misternoe/cheatbox/D-BRAKE - Haute42/R Series (UNTESTED BETA)/README.txt

CHEATBOX_PROJECT
D-BRAKE v2.0 for Haute42 R Series Controllers - BETA

/////////////
DISCLAIMER
/////////////

Use this product at your own risk. I am not responsible for any damages to you or your property. If you experience any pain or discomfort while using the D-BRAKE, please discontinue use immediately.

///////////////////////////////
COMPATIBILITY
///////////////////////////////

Unknown! This is basically a T-Series D-BRAKE with a shorter base. Design tweaks based on this post
https://x.com/helloneet/status/1823939648542138430

///////////////////////////////
THINGS TO KNOW BEFORE PRINTING
///////////////////////////////

UNTESTED

/////////////
PRINTER SETTINGS
/////////////

IMPORTANT -- Printing Orientation
The D-BRAKE looks best when printed upright, with the mount parallel to the build plate. Check the reference photo in the GitHub directory.

Infill: 10% to 25%

Layer height: 0.2 minimum

Build Plate Adhesion Type: Brim highly recommended due to the verticality of the printing orientation

Supports: Yes - Touching Buildplate

/////////////
PRINTING SERVICES: SIZING WHEN UPLOADED
/////////////

TBD

/////////////
INSTALLATION
/////////////
1. Remove plunger or keycap (see manufacturer for info on this if needed)
2. Mount D-BRAKE onto the button/microswitch

/////////////
REPORT BACK + ENJOY
/////////////

Let me know how you're enjoying this on Twitter or here on GitHub. Constructive feedback is always welcome. Give me a follow on Twitter @noe_perez_ to keep up with other projects like this and new Cheatbox Project designs for the Snackbox Micro, Hit Box, and other all-button controllers.

https://github.com/misternoe/cheatbox

/////////////
SHOUTOUTS
/////////////

@junkfoodarcades for making great products supporting the modding community

@NoGoodCitizen for spreading the gospel of the Cheatbox_Project to the FGC

Robear512 (@236Robear) for their dedication to bringing us a Qanba Gravity D-BRAKE

@helloneet for the R16 references

Anyone's that supported my on etsy or spread the word about cheatbox_project products!
