misternoe/cheatbox/D-BRAKE - Haute42/G Series/README.txt

CHEATBOX_PROJECT
D-BRAKE v2.0 for Haute42 G Series Controllers

/////////////
DISCLAIMER
/////////////

Use this product at your own risk. I am not responsible for any damages to you or your property. If you experience any pain or discomfort while using the D-BRAKE, please discontinue use immediately.

///////////////////////////////
COMPATIBILITY
///////////////////////////////

Works with:
G13/G16

Incompatible or unknown:
M-Series and S-Series - unknown but likely this is too large for it
T-Series - incompatible

///////////////////////////////
THINGS TO KNOW BEFORE PRINTING
///////////////////////////////

All testing conducted on a Haute42 G16

All test printing with a Bambu X1 Carbon

Materials tested:
PETG: Excellent output

/////////////
PRINTER SETTINGS
/////////////

IMPORTANT -- Printing Orientation
The D-BRAKE looks best when printed upright, with the mount parallel to the build plate. Check the reference photo in the GitHub directory.

Infill: 10% to 25%

Layer height: 0.2 minimum

Build Plate Adhesion Type: Brim highly recommended due to the verticality of the printing orientation

Supports: Yes - Touching Buildplate

/////////////
FINISHING
/////////////
If your printer is unable to produce a smooth print, it is recommended to sand down this print to provide a smoother and more comfortable surface. Use a high grit wet sandpaper (600 or higher). Please remember to take proper safety precautions to avoid inhalation by yourself and others in your vicinity.

/////////////
PRINTING SERVICES: SIZING WHEN UPLOADED
/////////////

TBD

/////////////
INSTALLATION
/////////////
1. Remove plunger or keycap (see manufacturer for info on this if needed)
2. Mount D-BRAKE onto the button/microswitch

/////////////
REPORT BACK + ENJOY
/////////////

Let me know how you're enjoying this on Twitter or here on GitHub. Constructive feedback is always welcome. Give me a follow on Twitter @noe_perez_ to keep up with other projects like this and new Cheatbox Project designs for the Snackbox Micro, Hit Box, and other all-button controllers.

https://github.com/misternoe/cheatbox

/////////////
SHOUTOUTS
/////////////

@junkfoodarcades for making great products supporting the modding community

@NoGoodCitizen for spreading the gospel of the Cheatbox_Project to the FGC

Robear512 (@236Robear) for their dedication to bringing us a Qanba Gravity D-BRAKE

@brainpipeFGC for the idea to explore and workshop the potential of the D-BRAKE + G16

Anyone's that supported my on etsy or spread the word about cheatbox_project products!
