misternoe/cheatbox/Snackbox Micro/ACCESSORIES/FOOTSIE/Original Artwork Case/README.txt

CHEATBOX_PROJECT
FOOTSIE v1.0
For Snackbox Micro Artwork Case

/////////////
DISCLAIMER
/////////////

Use this product at your own risk. I am not responsible for any damages to you or your property.

///////////////////////////////
THINGS TO KNOW BEFORE PRINTING
///////////////////////////////

All testing conducted on a Dremel DigiLab 3D45 with a stock pre-2023 Snackbox Micro Artwork Case.

Materials tested:
PLA: Excellent output

Important:
Make sure that your 3D printer is configured properly before printing this accessory. Due to the thin nature of this product, ensuring that the first few layers print cleanly will ensure a stronger end product.

/////////////
PRINTER SETTINGS
/////////////
15% Infill recommended

Layer height
0.3 or 0.34 look great and print quickly. 0.34 looks best to me personally.

/////////////
SIZING
/////////////

FOOTSIE-LEFT
X = 168mm
Y = 127.25mm
Z = 15mm

FOOTSIE-RIGHT
X = 168mm
Y = 127.25mm
Z = 15mm

FOOTSIE-SINGLE
X = 336mm
Y = 127.25mm
Z = 15mm

/////////////
INSTALLATION
/////////////
1. Unscrew backplate of Snackbox Micro

2. Install The Footsie between backplate and Snackbox Micro Artwork Case. The Footsie is to be “sandwiched” between these two components.

3. Insert screws and be sure to not over-tighten

/////////////
REPORT BACK + ENJOY
/////////////

Let me know how testing is going on Twitter or here on GitHub. Give me a follow on Twitter @noe_perez_ to keep up with other projects like this and new Cheatbox Project designs for the Snackbox Micro and other all-button controllers.

https://github.com/misternoe/cheatbox
