misternoe/cheatbox/Snackbox Micro/ACCESSORIES/FOOTSIE/FOOTSIE - ORIGINAL/Micro XL/README.txt

CHEATBOX_PROJECT
FOOTSIE v1.0
For Snackbox Micro XL Case

/////////////
DISCLAIMER
/////////////

Use this product at your own risk. I am not responsible for any damages to you or your property.

///////////////////////////////
THINGS TO KNOW BEFORE PRINTING
///////////////////////////////

All testing conducted on a Dremel DigiLab 3D45 with a stock 2023 Snackbox Micro XL.

Materials tested:
PLA: Excellent output

Important:
Make sure that your 3D printer is configured properly before printing this accessory. Due to the thin nature of this product, ensuring that the first few layers print cleanly will ensure a stronger end product.

/////////////
PRINTER SETTINGS
/////////////
15% Infill recommended

Layer height
0.3 or 0.34 look great and print quickly. 0.34 looks best to me personally.

/////////////
SIZING
/////////////

FOOTSIE-LEFT
X = 199.25mm
Y = 143.875mm
Z = 13.625mm

FOOTSIE-RIGHT
X = 199.25mm
Y = 143.875mm
Z = 13.625mm

/////////////
INSTALLATION
/////////////
1. Unscrew backplate of Snackbox Micro XL Case

2. Install The Footsie between backplate and Snackbox Micro XL Case. The Footsie is to be “sandwiched” between these two components.

3. Insert screws and be sure to not over-tighten

/////////////
REPORT BACK + ENJOY
/////////////

Let me know how testing is going on Twitter or here on GitHub. Give me a follow on Twitter @noe_perez_ to keep up with other projects like this and new Cheatbox Project designs for the Snackbox Micro and other all-button controllers.

https://github.com/misternoe/cheatbox
