misternoe/cheatbox/Snackbox Micro/ACCESSORIES/FOOTSIE/FOOTSIE - ORIGINAL/New Artwork Case and One Piece Case/README.txt

CHEATBOX_PROJECT
FOOTSIE v1.0
For Snackbox Micro One Piece Case

/////////////
DISCLAIMER
/////////////

Use this product at your own risk. I am not responsible for any damages to you or your property.

///////////////////////////////
THINGS TO KNOW BEFORE PRINTING
///////////////////////////////

All testing conducted on a Dremel DigiLab 3D45 with a stock 2023 Snackbox One Piece Case - Clear.

Materials tested:
PLA: Excellent output

Important:
Make sure that your 3D printer is configured properly before printing this accessory. Due to the thin nature of this product, ensuring that the first few layers print cleanly will ensure a stronger end product.

/////////////
PRINTER SETTINGS
/////////////
15% Infill recommended

Layer height
0.3 or 0.34 look great and print quickly. 0.34 looks best to me personally.

/////////////
SIZING
/////////////

FOOTSIE-LEFT
X = 166.125mm
Y = 129mm
Z = 14.5mm

FOOTSIE-RIGHT
X = 166.25mm
Y = 129mm
Z = 14.5mm

FOOTSIE-SINGLE
X = 330mm
Y = 129mm
Z = 14.5mm

/////////////
INSTALLATION
/////////////
1. Unscrew backplate of Snackbox Micro One Piece Case

2. Install The Footsie between backplate and Snackbox Micro One Piece Case. The Footsie is to be “sandwiched” between these two components.

3. Insert screws and be sure to not over-tighten

/////////////
REPORT BACK + ENJOY
/////////////

Let me know how testing is going on Twitter or here on GitHub. Give me a follow on Twitter @noe_perez_ to keep up with other projects like this and new Cheatbox Project designs for the Snackbox Micro and other all-button controllers.

https://github.com/misternoe/cheatbox
