misternoe/cheatbox/Hitbox/cheatbox-hitbox-input-trainer.png

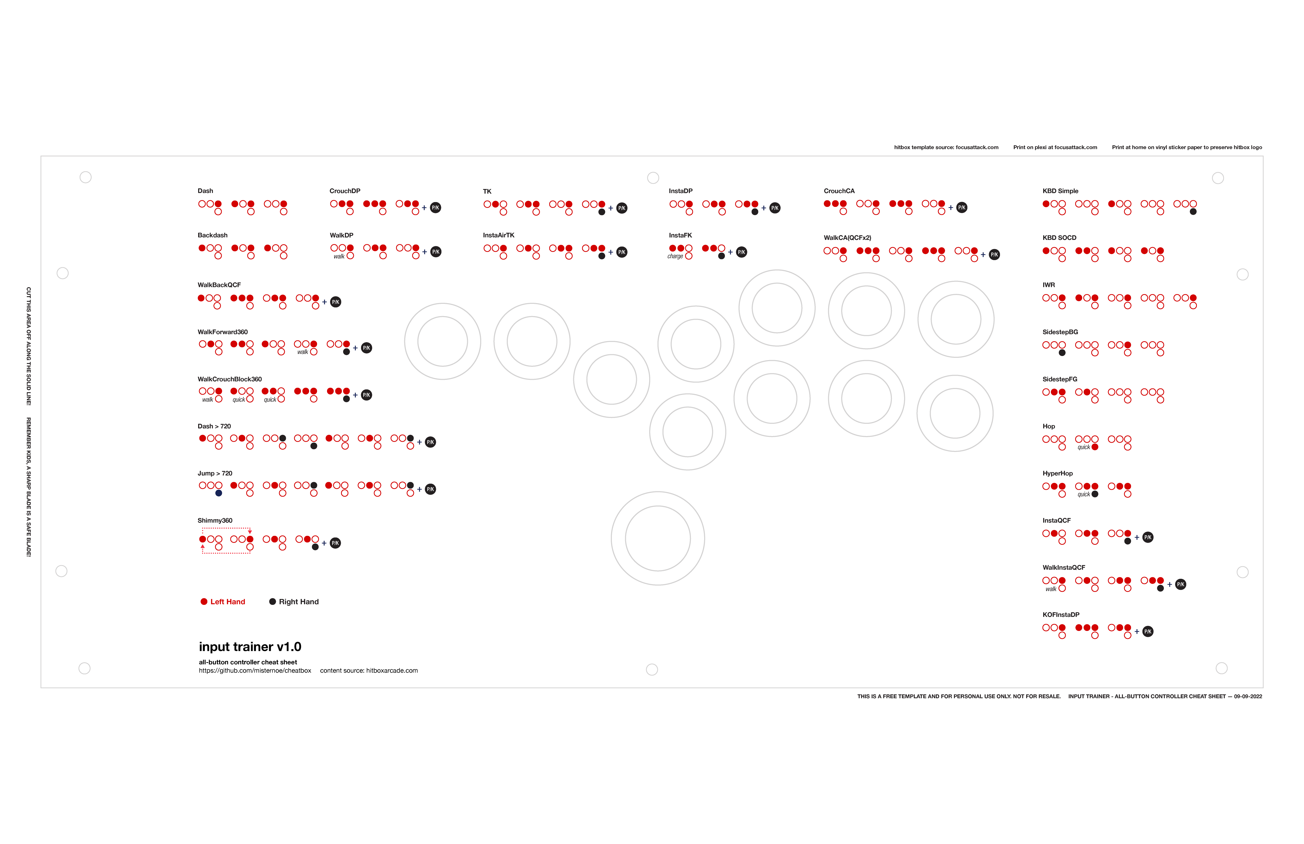
Hitbox/cheatbox-hitbox-input-trainer.png
