misternoe/cheatbox/Snackbox Micro/SFV/cheatboxmicro-sfv-jur-8.5x11-300DPI.png

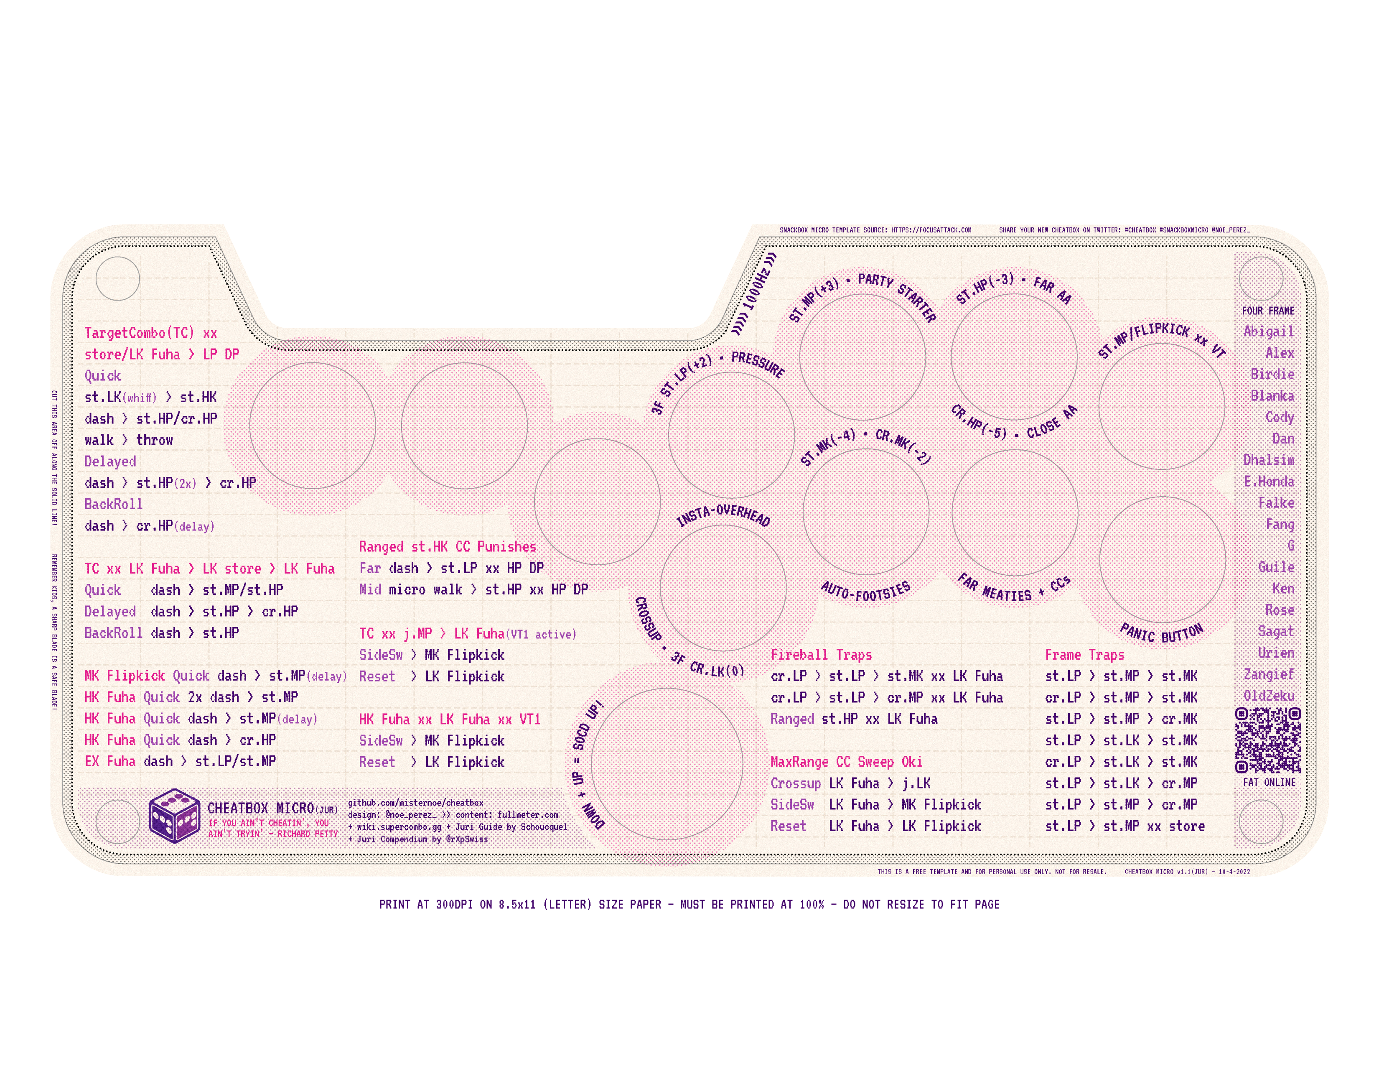
Snackbox Micro/SFV/cheatboxmicro-sfv-jur-8.5x11-300DPI.png
