misternoe/cheatbox/Snackbox Micro/SG/cheatboxmicro-sg-bgbnd-8.5x11-300DPI.png

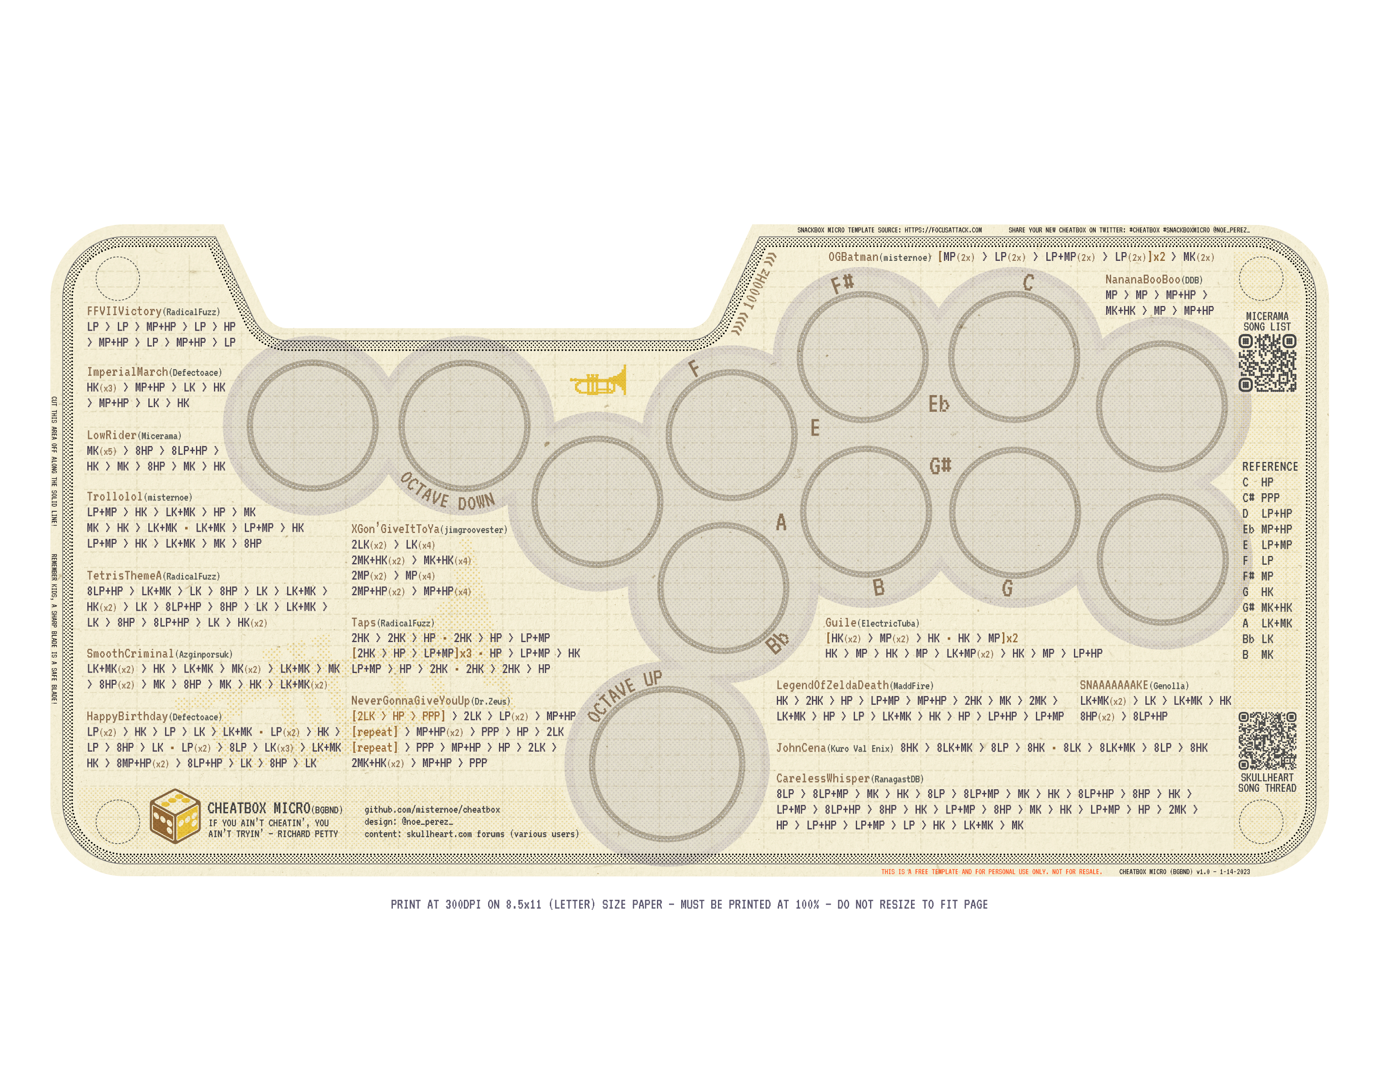
Snackbox Micro/SG/cheatboxmicro-sg-bgbnd-8.5x11-300DPI.png
