misternoe/cheatbox/Snackbox Micro/SOCD/cheatboxmicro-socd-brbrshp-classic-8.5x11-300DPI.png

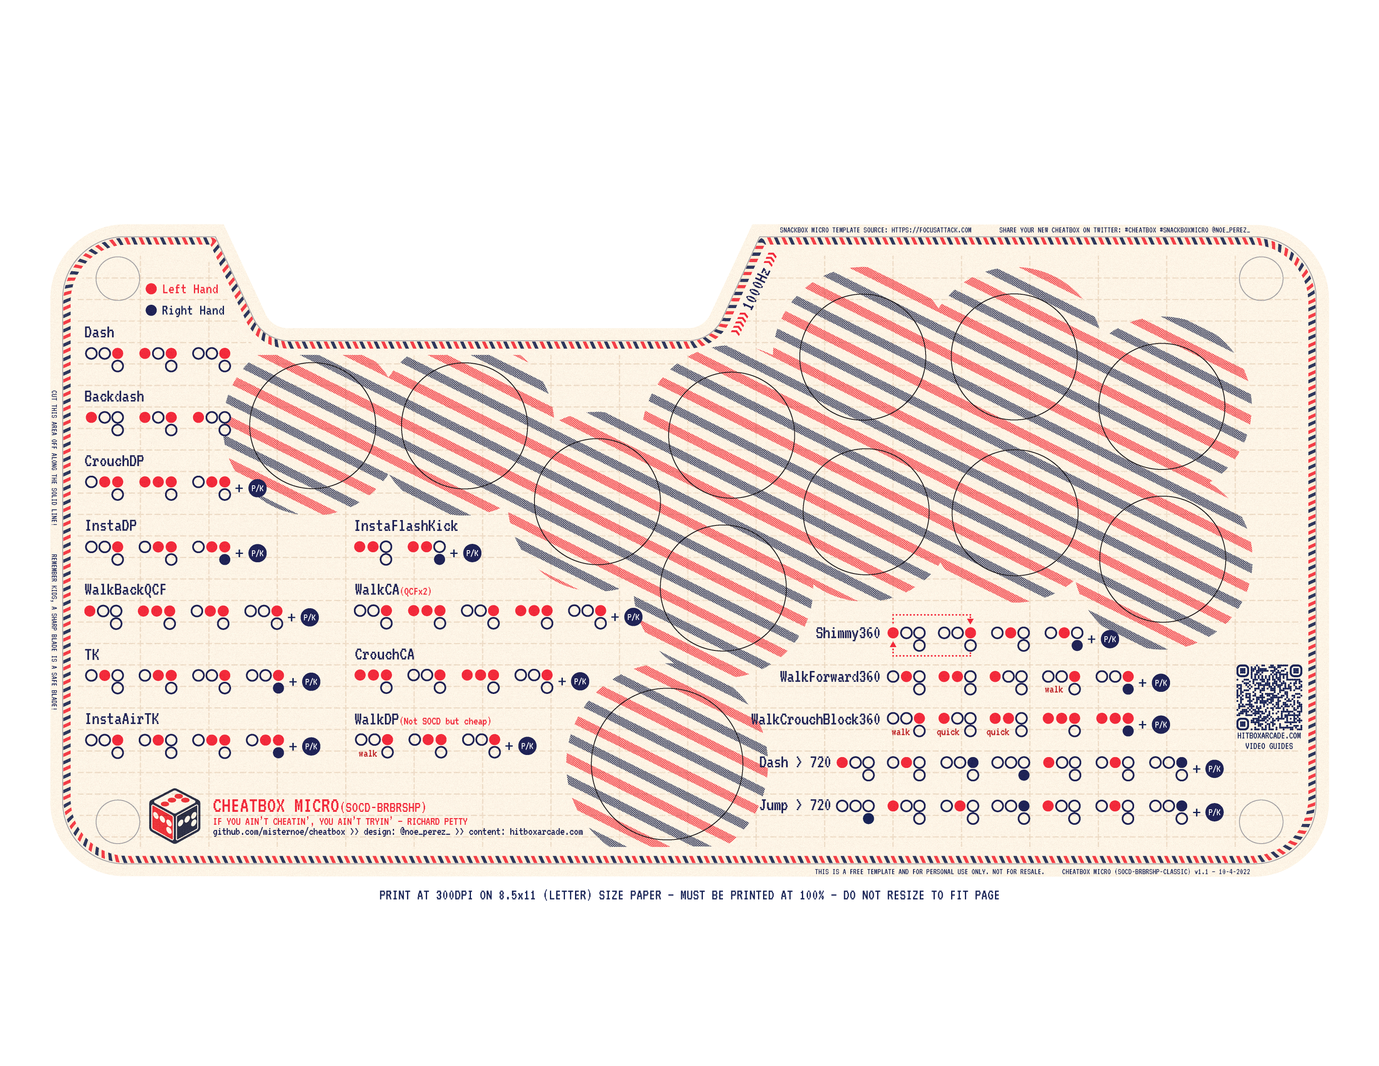
Snackbox Micro/SOCD/cheatboxmicro-socd-brbrshp-classic-8.5x11-300DPI.png
