misternoe/cheatbox/D-BRAKE/remix-cheatbox-project-dbrake-qanba-gravity-24mm-size11.stl

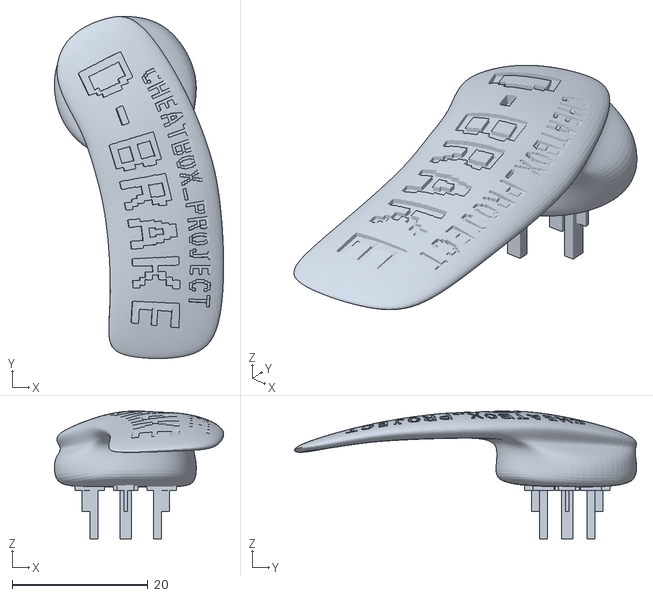
[picture p29: CAD file, 2024-03-22]
D-BRAKE/remix-cheatbox-project-dbrake-qanba-gravity-24mm-size11.stl
24.9 x 50.3 x 18.8
