misternoe/cheatbox/FOOTSIE - NEW/cheatbox-project-footsie-left.stl

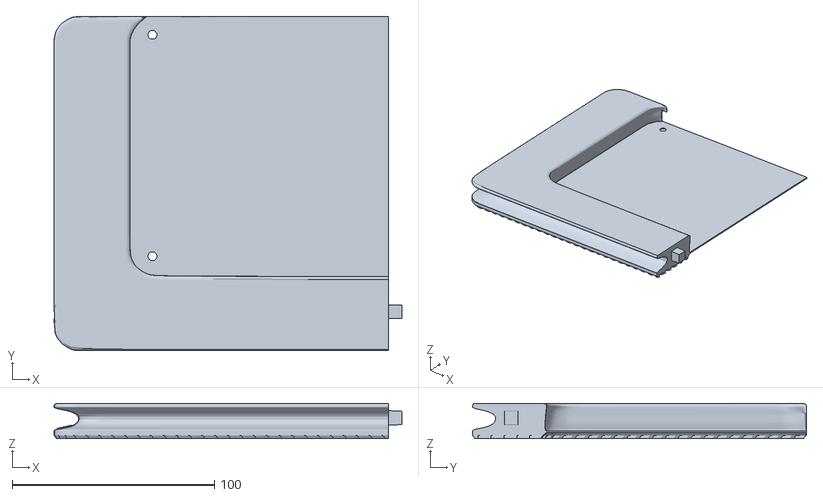
[picture p30: CAD file, 2025-10-26]
FOOTSIE - NEW/cheatbox-project-footsie-left.stl
172.1 x 165.1 x 17.5
