misternoe/cheatbox/Haute42 B16/cheatboxproject-B16-faceplate-face-up.stl

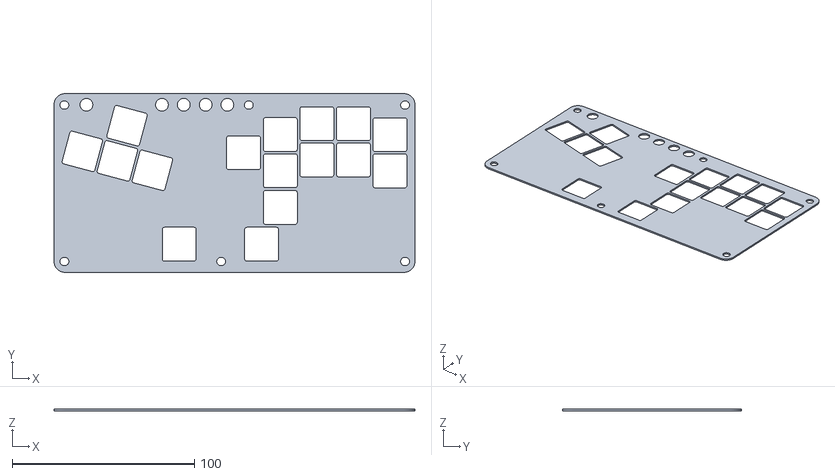
[picture p31: CAD file, 2025-02-02]
Haute42 B16/cheatboxproject-B16-faceplate-face-up.stl
198.0 x 98.0 x 0.96
