misternoe/cheatbox/Snackbox Micro/ACCESSORIES/FOOTSIE/FOOTSIE - ORIGINAL/Micro XL/micro-xl-footsie-right.stl

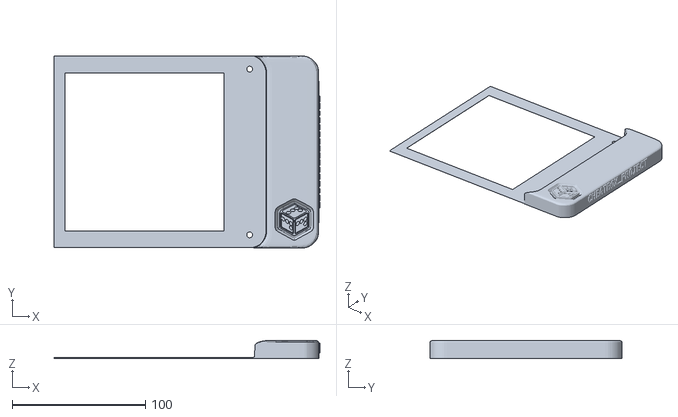
[picture p32: CAD file, 2023-04-07]
Snackbox Micro/ACCESSORIES/FOOTSIE/FOOTSIE - ORIGINAL/Micro XL/micro-xl-footsie-right.stl
199.3 x 143.9 x 13.6
