misternoe/cheatbox/Snackbox Micro/ACCESSORIES/FOOTSIE/FOOTSIE - ORIGINAL/Needs Testing/OG Snackbox Micro/og-micro-footsie-right.stl

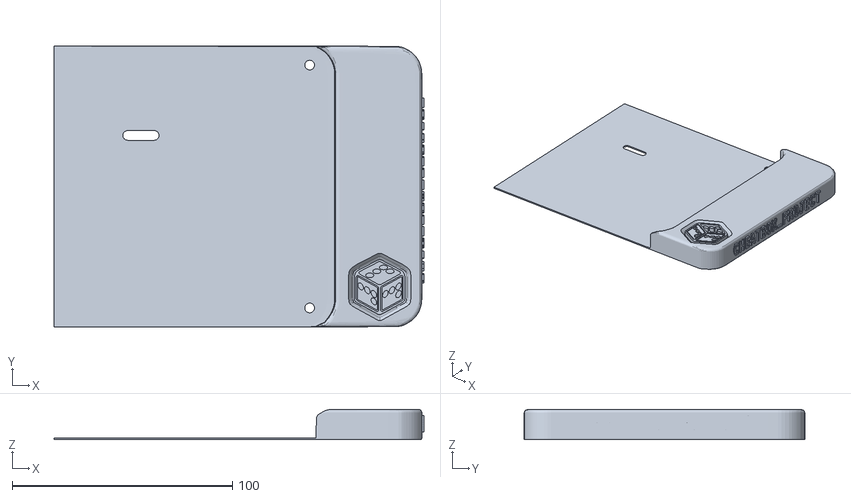
[picture p33: CAD file, 2023-03-16]
Snackbox Micro/ACCESSORIES/FOOTSIE/FOOTSIE - ORIGINAL/Needs Testing/OG Snackbox Micro/og-micro-footsie-right.stl
168.0 x 127.4 x 13.8
