misternoe/cheatbox/Snackbox Micro/ACCESSORIES/FOOTSIE/Original Artwork Case/original-artworkcase-footsie-left.stl

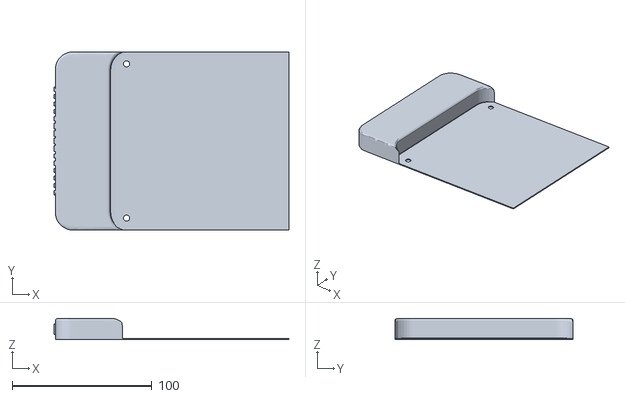
[picture p34: CAD file, 2023-03-15]
Snackbox Micro/ACCESSORIES/FOOTSIE/Original Artwork Case/original-artworkcase-footsie-left.stl
168.0 x 127.4 x 15.1
