misternoe/cheatbox/SWORL/Hole Plugs/sw-plug-below-artwork.stl

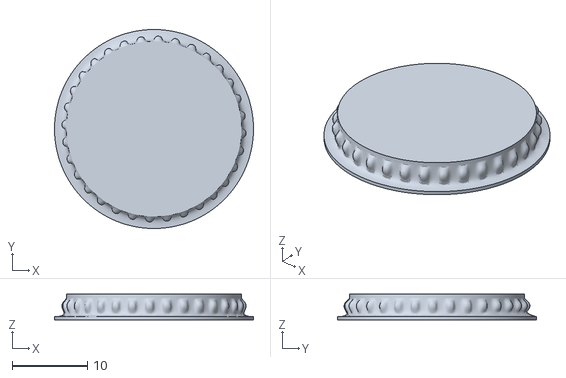
[picture p35: CAD file, 2025-09-05]
SWORL/Hole Plugs/sw-plug-below-artwork.stl
26.5 x 26.5 x 3.41
