misternoe/cheatbox/D-BRAKE - Flashtap/dbrake-flashtap24-09mm-CE.stl

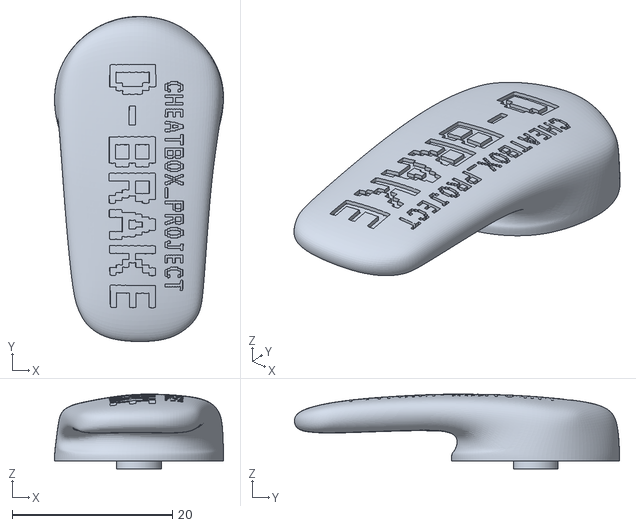
[picture p36: CAD file, 2026-08-28]
D-BRAKE - Flashtap/dbrake-flashtap24-09mm-CE.stl
21.1 x 40.6 x 9.33
