misternoe/cheatbox/D-BRAKE/remix-cheatbox-project-dbrake-qanba-gravity-30mm-size11.stl

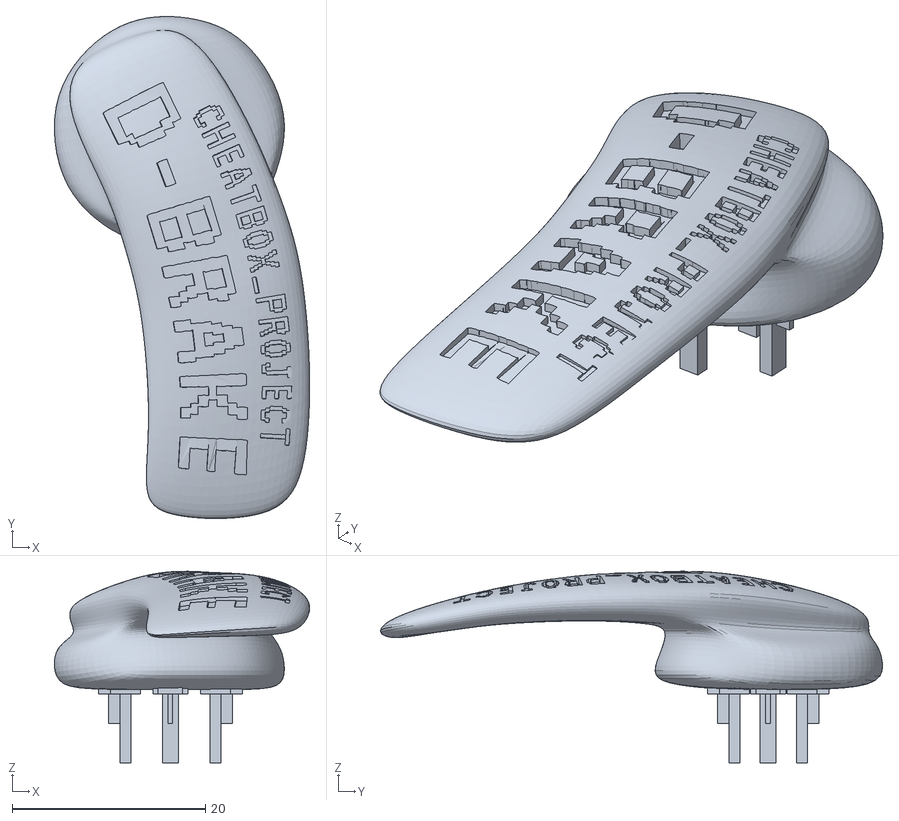
[picture p37: CAD file, 2024-03-12]
D-BRAKE/remix-cheatbox-project-dbrake-qanba-gravity-30mm-size11.stl
26.4 x 52.0 x 19.8
