misternoe/cheatbox/Snackbox Micro/ACCESSORIES/FOOTSIE/FOOTSIE - ORIGINAL/Needs Testing/OG Snackbox Micro/og-micro-footsie-left.stl

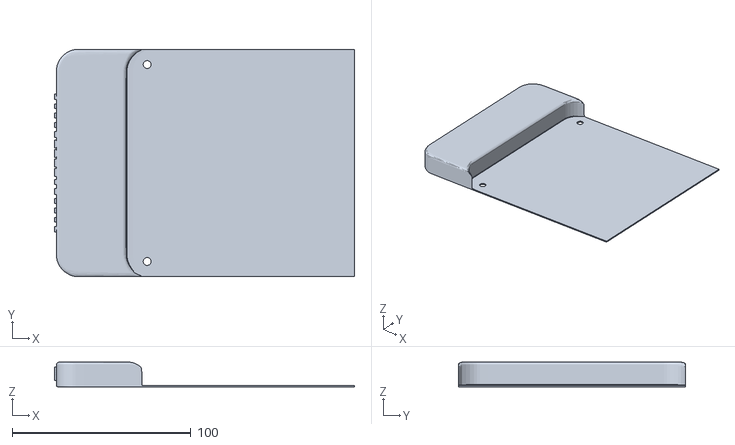
[picture p38: CAD file, 2023-03-16]
Snackbox Micro/ACCESSORIES/FOOTSIE/FOOTSIE - ORIGINAL/Needs Testing/OG Snackbox Micro/og-micro-footsie-left.stl
168.0 x 127.4 x 13.8
