misternoe/cheatbox/D-BRAKE/remix-robear512-dbrake-qanba-gravity-30mm.stl

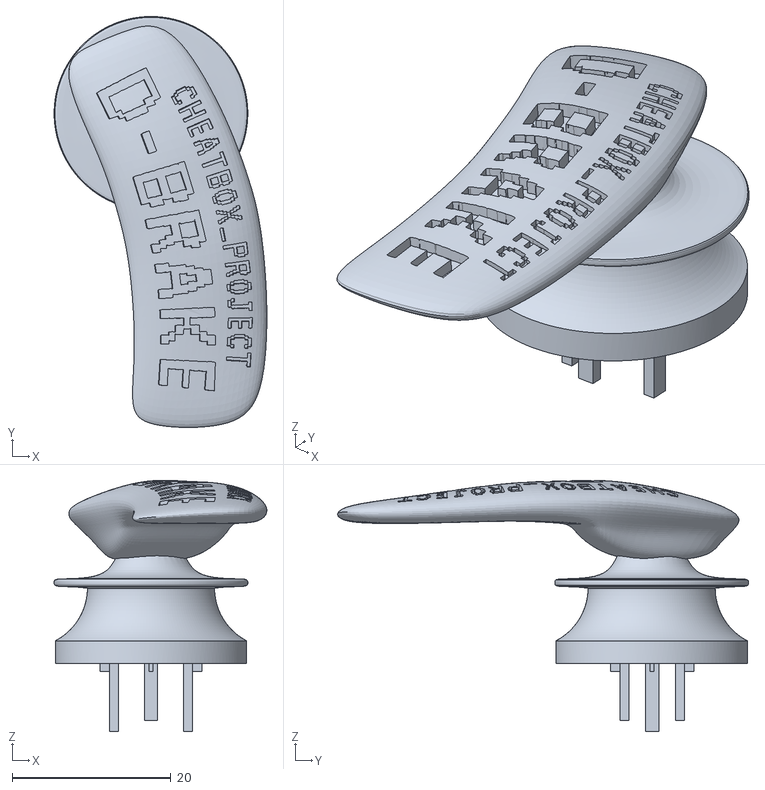
[picture p40: CAD file, 2024-03-12]
D-BRAKE/remix-robear512-dbrake-qanba-gravity-30mm.stl
26.8 x 51.7 x 31.6
