misternoe/cheatbox/D-BRAKE/cheatbox-project-dbrake-snackboxmicro-kailh-choc-v1-thickerstem.stl

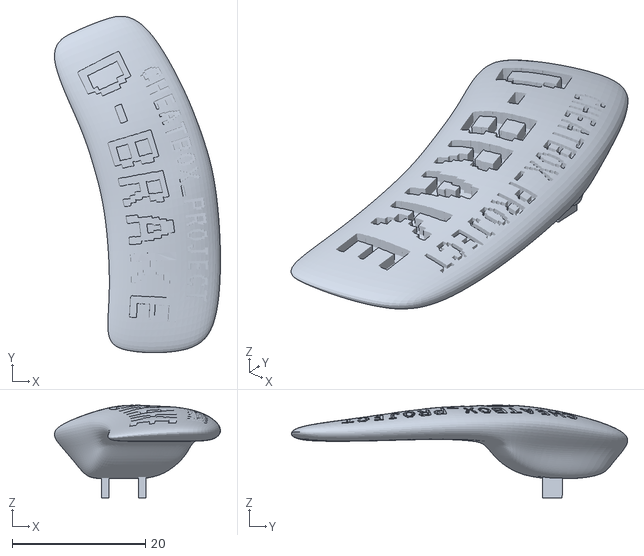
[picture p41: CAD file, 2023-06-09]
D-BRAKE/cheatbox-project-dbrake-snackboxmicro-kailh-choc-v1-thickerstem.stl
24.9 x 50.5 x 13.9
