misternoe/cheatbox/D-BRAKE/cheatbox-project-dbrake-sanwa-seimitsu-30mm-size10.stl

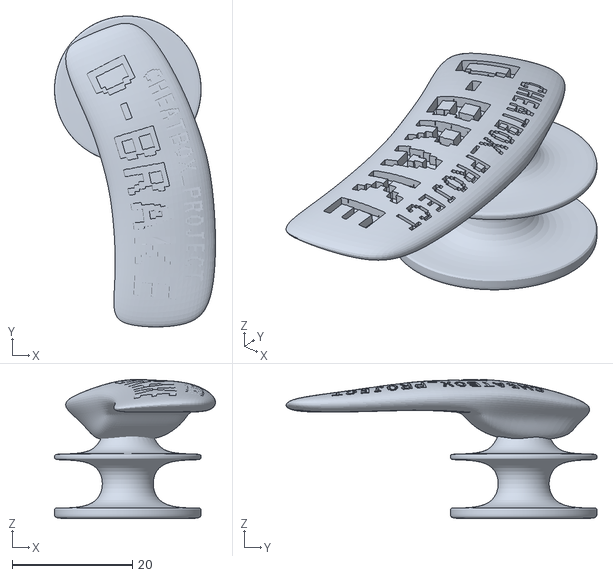
[picture p42: CAD file, 2023-06-02]
D-BRAKE/cheatbox-project-dbrake-sanwa-seimitsu-30mm-size10.stl
26.8 x 51.7 x 23.1
