misternoe/cheatbox/D-BRAKE/cheatbox-project-dbrake-sanwa-seimitsu-30mm-size11.stl

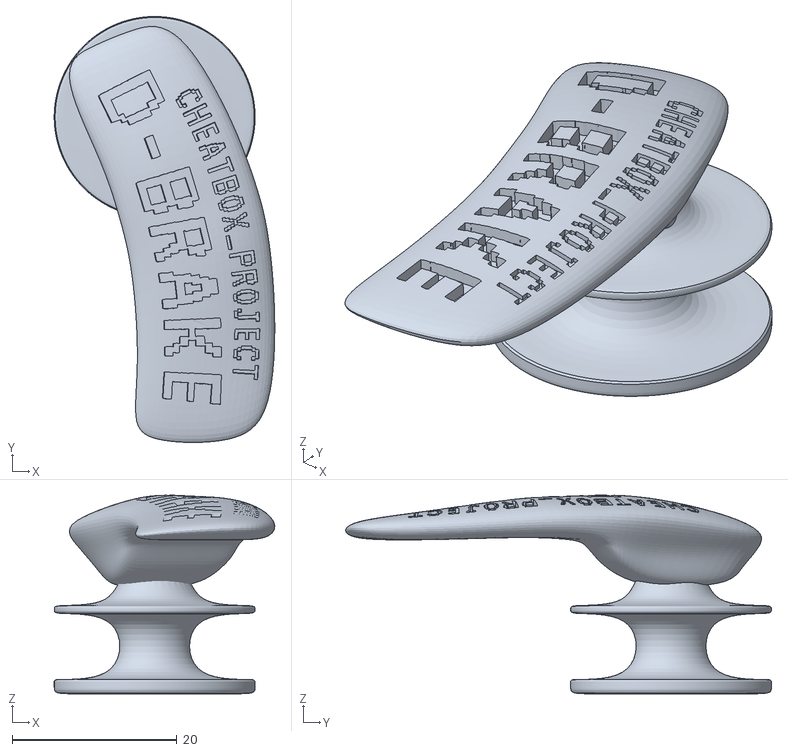
[picture p43: CAD file, 2023-06-02]
D-BRAKE/cheatbox-project-dbrake-sanwa-seimitsu-30mm-size11.stl
26.8 x 51.7 x 24.1
