misternoe/cheatbox/D-BRAKE/cheatbox-project-dbrake-cherrymx-10mm.stl

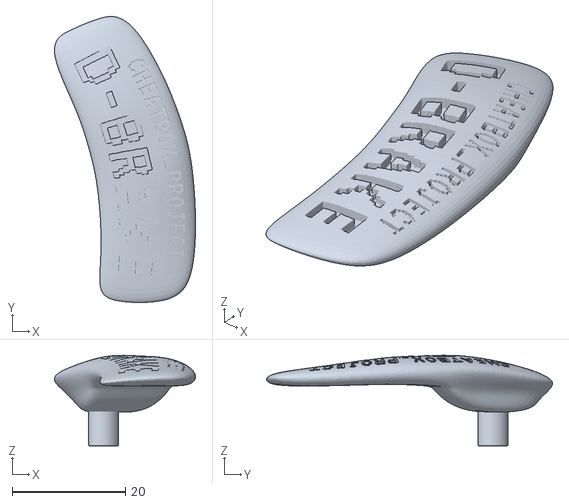
[picture p44: CAD file, 2023-05-29]
D-BRAKE/cheatbox-project-dbrake-cherrymx-10mm.stl
24.9 x 50.5 x 16.0
