misternoe/cheatbox/D-BRAKE/cheatbox-project-dbrake-cherrymx-11mm.stl

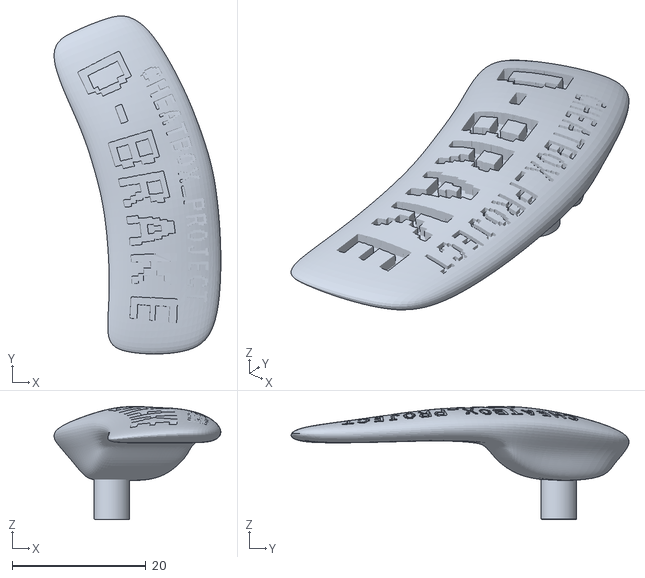
[picture p45: CAD file, 2023-05-29]
D-BRAKE/cheatbox-project-dbrake-cherrymx-11mm.stl
24.9 x 50.5 x 16.9
