misternoe/cheatbox/D-BRAKE/dbrake-gravity-printing-orientation.jpg

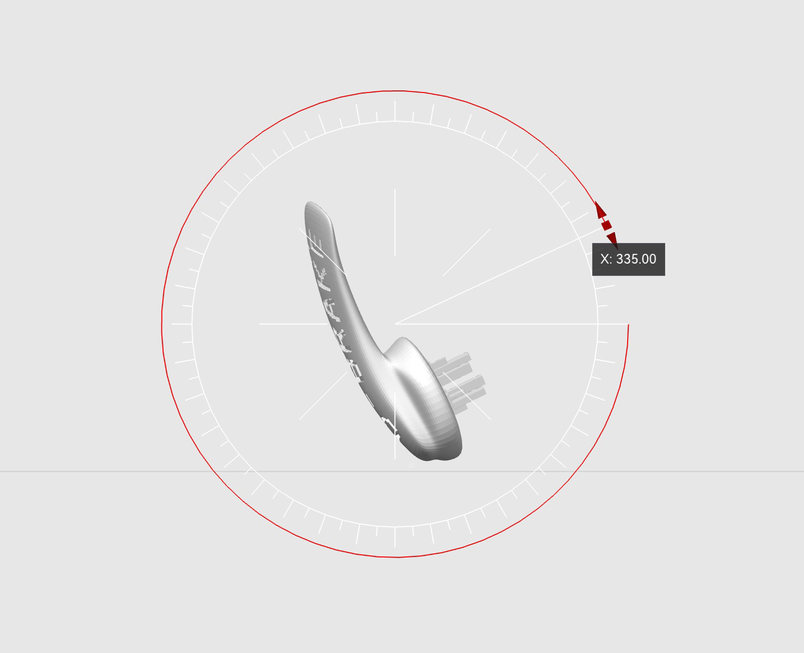
D-BRAKE/dbrake-gravity-printing-orientation.jpg
