misternoe/cheatbox/D-BRAKE/dbrake-printing-orientation.jpg

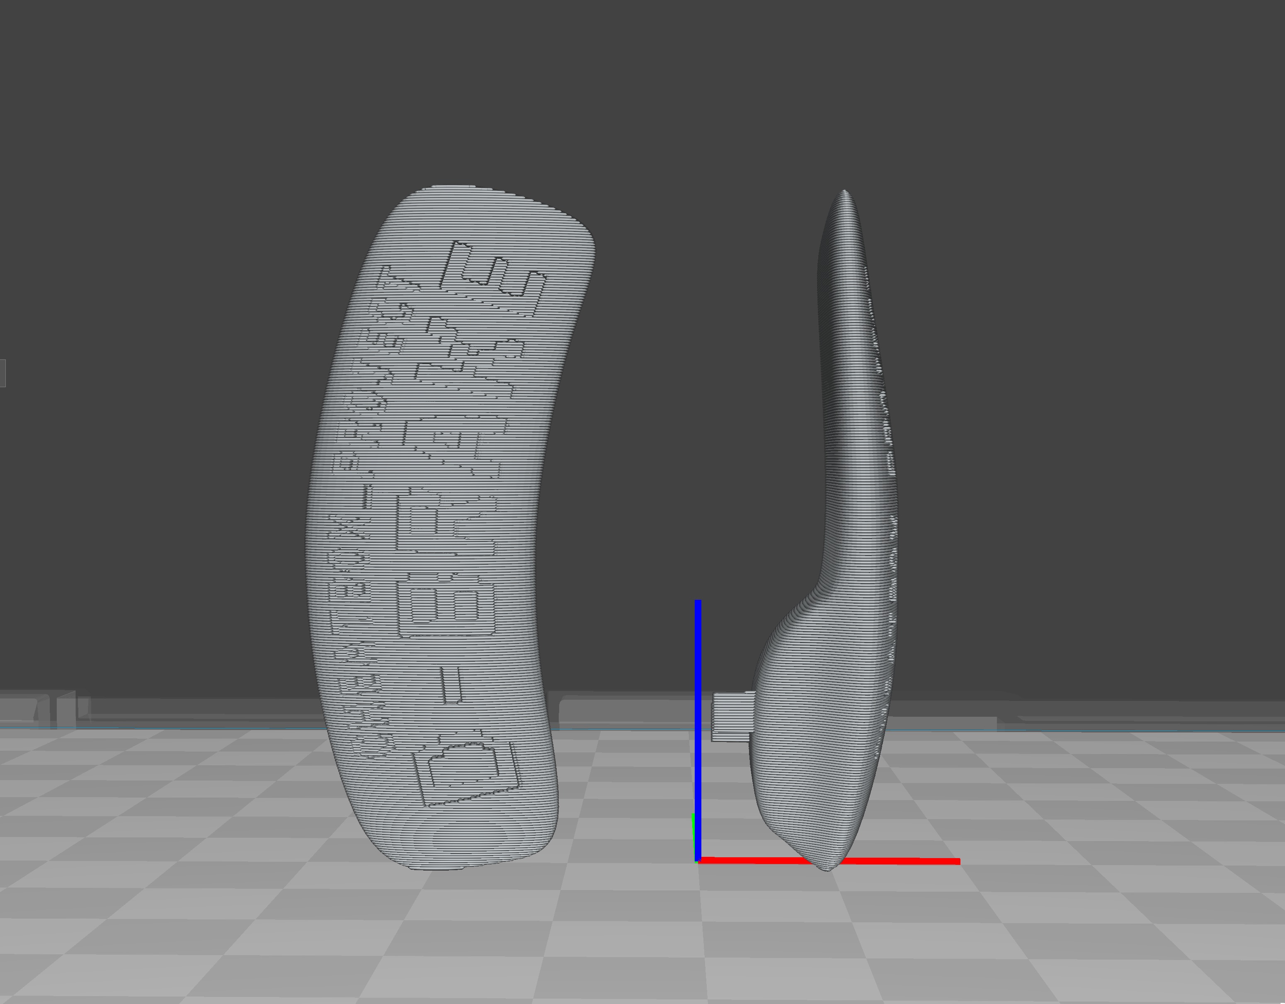
D-BRAKE/dbrake-printing-orientation.jpg
