misternoe/cheatbox/FOOTSIE - NEW/footsie-printing-orientation-for-small-printers.jpg

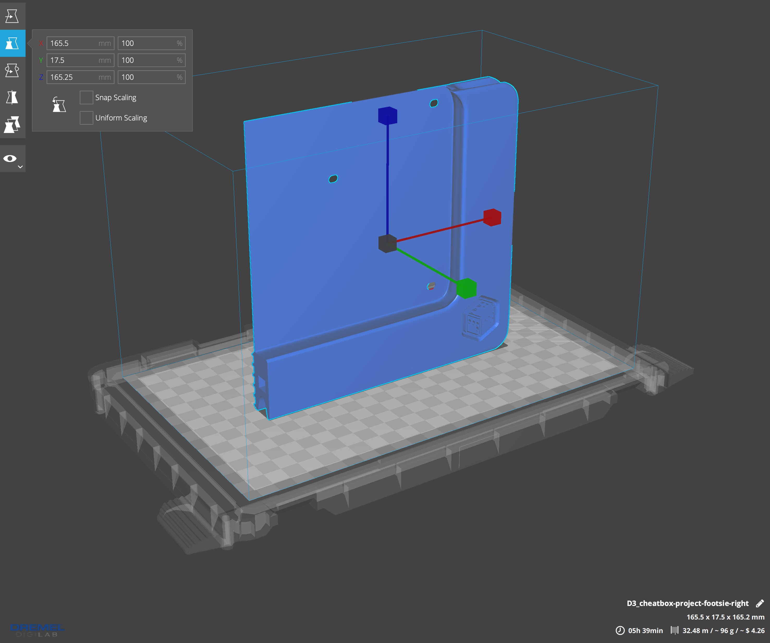
FOOTSIE - NEW/footsie-printing-orientation-for-small-printers.jpg
